Hypnopompia/photon-desk/pcb/board-outline.png

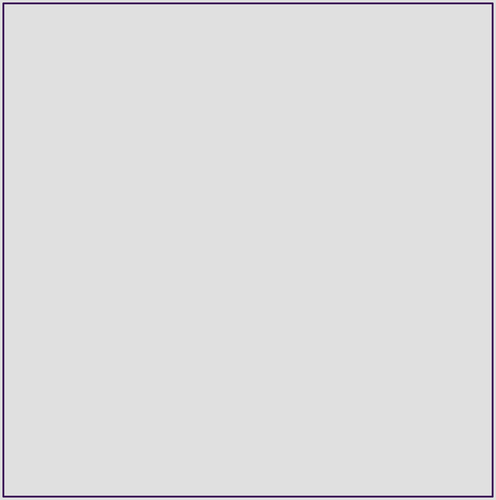
pcb/board-outline.png
