Hypnopompia/photon-desk/pcb/bottom-layer.png

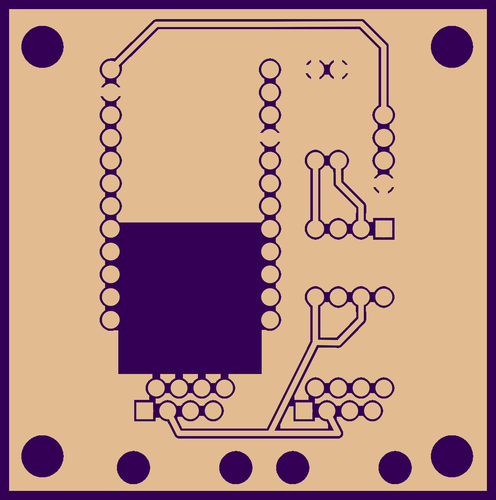
pcb/bottom-layer.png
