Hypnopompia/photon-desk/pcb/drills.png

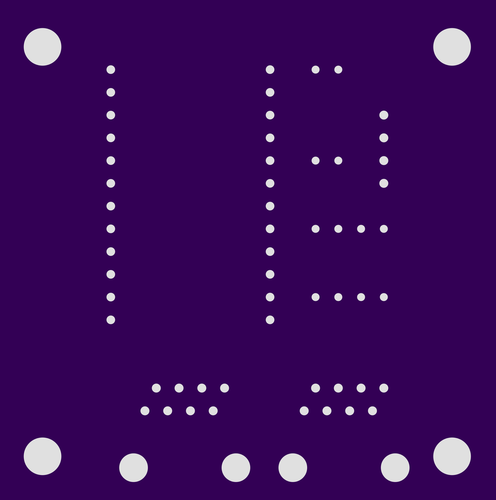
pcb/drills.png
