Hypnopompia/photon-desk/pcb/pdf/photon-desk_etch_silk_bottom.pdf

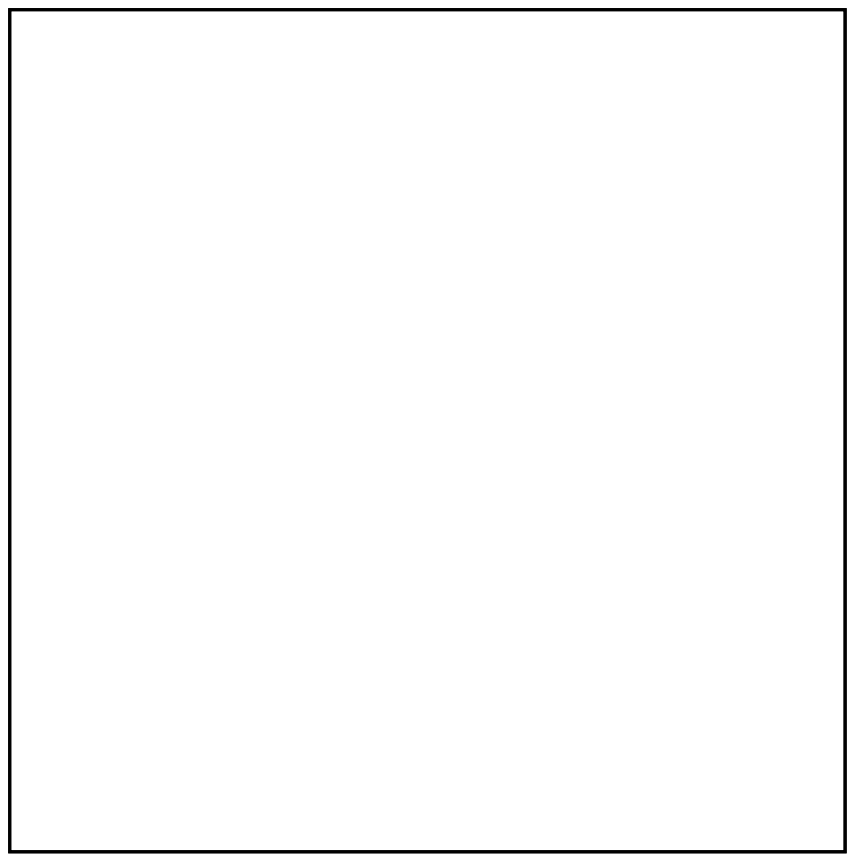
[picture p20: page 1]
