Hypnopompia/photon-desk/pcb/pdf/photon-desk_etch_silk_bottom_mirror.pdf

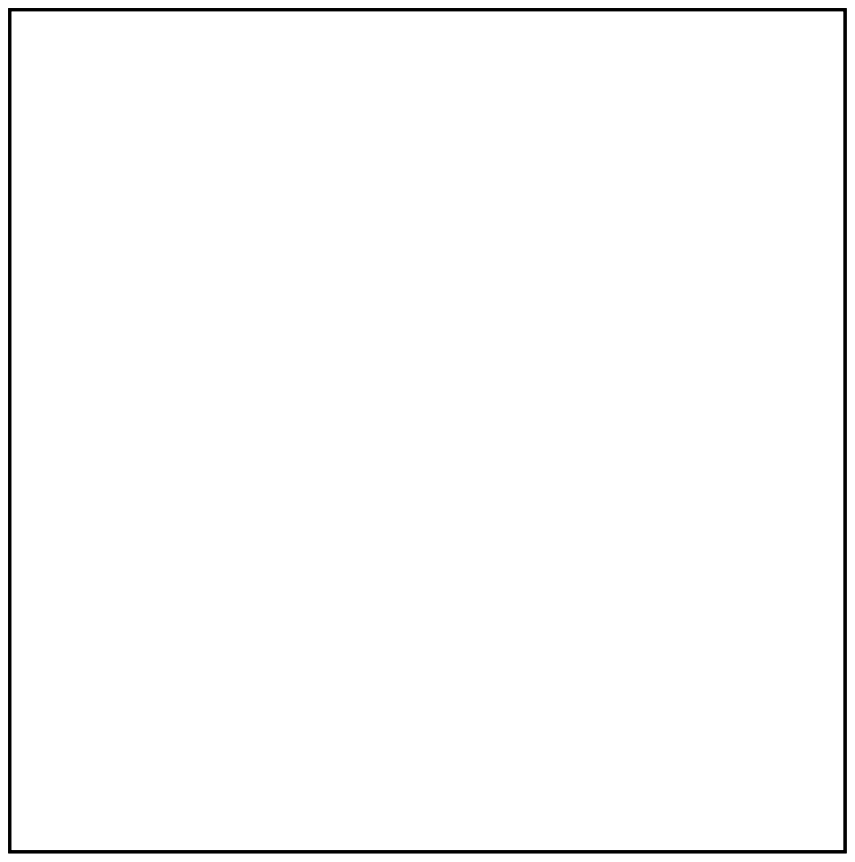
[picture p21: page 1]
