Hypnopompia/photon-desk/pcb/pdf/photon-desk_etch_silk_top.pdf

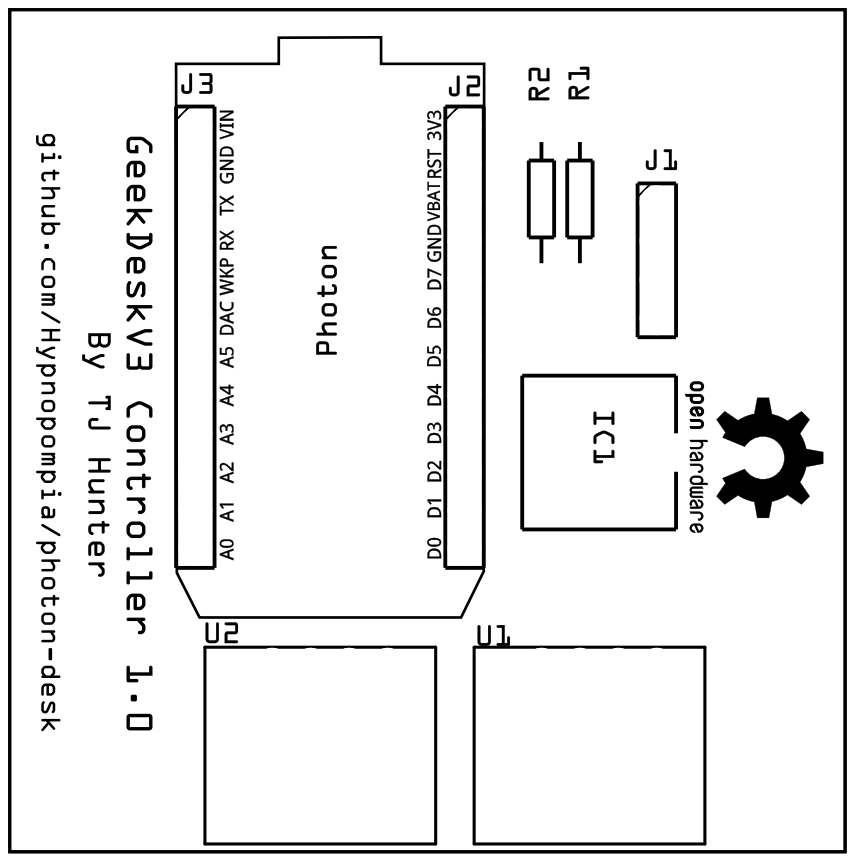
[picture p22: page 1]
