Hypnopompia/photon-desk/pcb/pdf/photon-desk_etch_silk_top_mirror.pdf

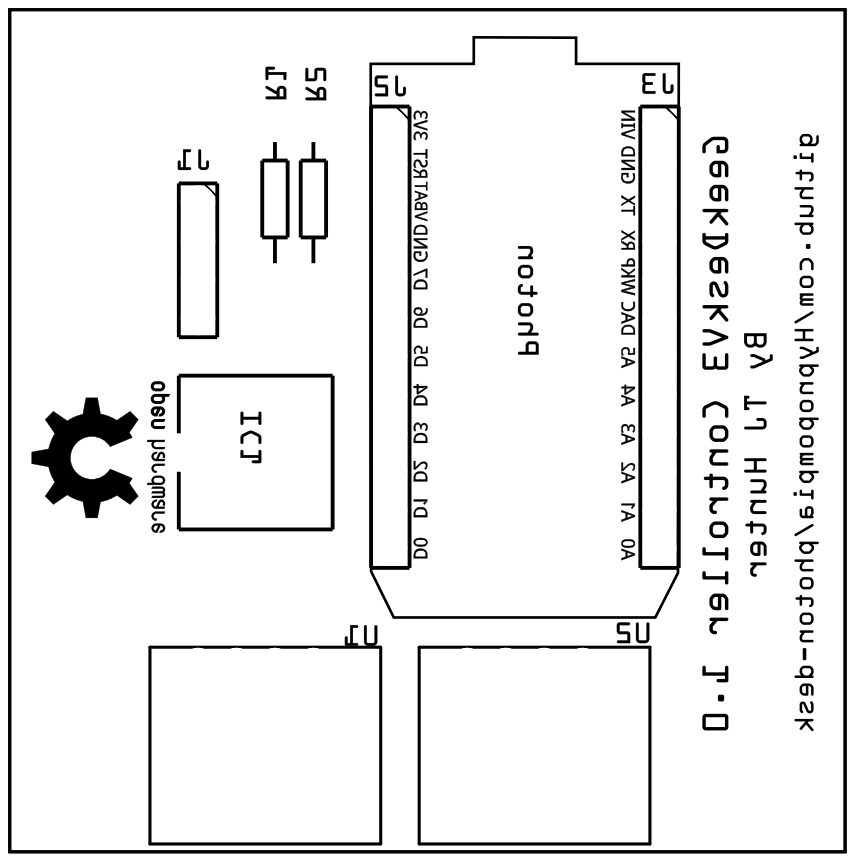
[picture p23: page 1]
